tensorway/2000transistors/src/4_lines_umemory.kicad_pcb

## KiCad design src/4_lines_umemory.kicad_pcb (2023-10-25)

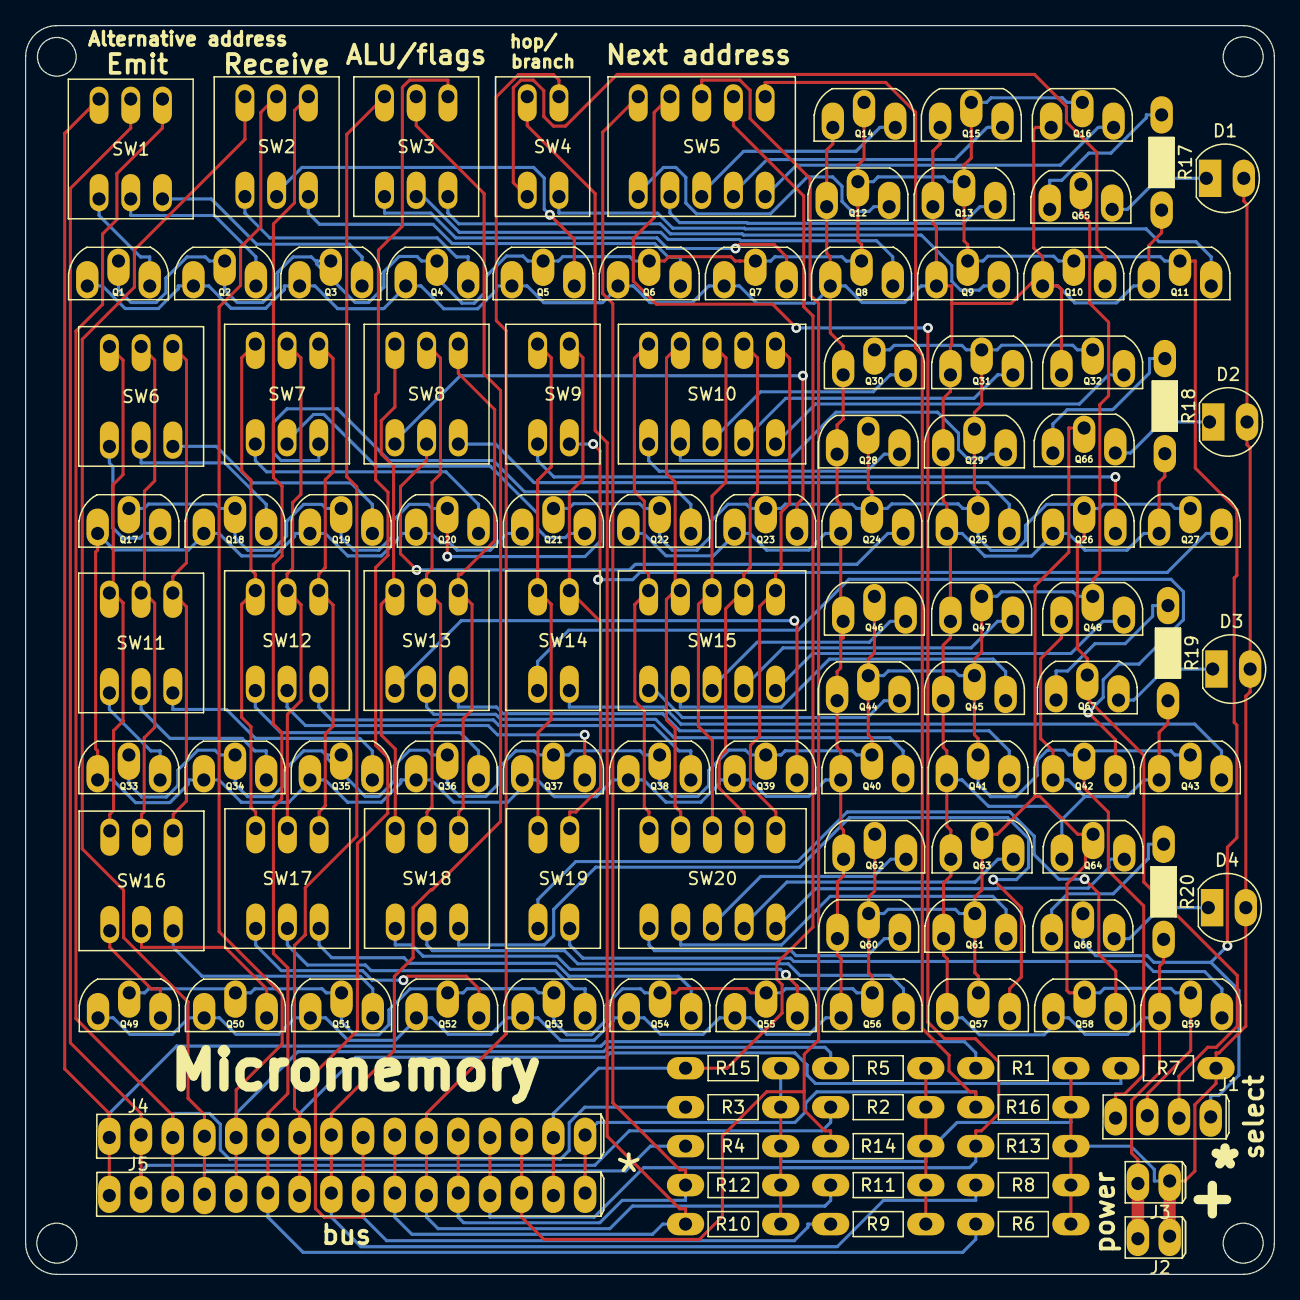
[picture p17: board 4_lines_umemory.kicad_pcb from above]

Board: 2 copper layers, 100.0 x 100.0 mm, 117 parts (0 on the bottom side), 110 nets.

Parts:
D1, D2, D3, D4: LED; led_5mm_tight
J1: Conn_01x04_Male; 4pin_tight
J2, J3: Conn_01x02_Male; 2pin_tight
J4, J5: Conn_01x16_Male; 16pin_tight
Q1, Q2, Q3, Q4, Q5, Q6, Q7, Q8, Q9, Q10, Q11, Q12, Q13, Q14, Q15, Q16, Q17, Q18, Q19, Q20, Q21, Q22, Q23, Q24, Q25, Q26, Q27, Q28, Q29, Q30, Q31, Q32, Q33, Q34, Q35, Q36, Q37, Q38, Q39, Q40, Q41, Q42, Q43, Q44, Q45, Q46, Q47, Q48, Q49, Q50, Q51, Q52, Q53, Q54, Q55, Q56, Q57, Q58, Q59, Q60, Q61, Q62, Q63, Q64, Q65, Q66, Q67, Q68: 2N7000; 2n7000_tight
R1, R2, R3, R4, R5, R6, R7, R8, R9, R10, R11, R12, R13, R14, R15, R16: R; resistor_tight
R17, R18, R19, R20: R; resistor_led_tight
SW1, SW2, SW3, SW6, SW7, SW8, SW11, SW12, SW13, SW16, SW17, SW18: SW_DIP_x03; dip3_switch
SW4, SW9, SW14, SW19: SW_DIP_x02; dip2_switch
SW5, SW10, SW15, SW20: SW_DIP_x05; dip5_switch

Connections:
+5V: D1.2, D2.2, D3.2, D4.2, J2.1, J3.1, R1.1, R2.1, R3.1, R4.1, R5.1, R6.1, R7.1, R8.1, R9.1, R10.1, R11.1, R12.1, R13.1, R14.1, R15.1, R16.1
/Sheet63D9F596/a: J4.1, J5.1, R1.2, SW1.3
/Sheet63D9F596/b: J4.2, J5.2, R2.2, SW1.2
/Sheet63D9F596/c: J4.3, J5.3, R3.2, SW1.1
/Sheet63D9F596/d: J4.4, J5.4, R4.2, SW2.3
/Sheet63D9F596/e: J4.5, J5.5, R5.2, SW2.2
/Sheet63D9F596/enable: J1.4, Q1.2, Q2.2, Q3.2, Q4.2, Q5.2, Q6.2, Q7.2, Q8.2, Q9.2, Q10.2, Q11.2, Q12.2, Q13.2, Q14.2, Q15.2, Q16.2, Q68.2
/Sheet63D9F596/f: J4.6, J5.6, R6.2, SW2.1
/Sheet63D9F596/g: J4.7, J5.7, R7.2, SW3.3
/Sheet63D9F596/h: J4.8, J5.8, R8.2, SW3.2
/Sheet63D9F596/i: J4.9, J5.9, R9.2, SW3.1
/Sheet63D9F596/j: J4.10, J5.10, R10.2, SW4.2
/Sheet63D9F596/k: J4.11, J5.11, R11.2, SW4.1
/Sheet63D9F596/l: J4.12, J5.12, R12.2, SW5.5
/Sheet63D9F596/m: J4.13, J5.13, R13.2, SW5.4
/Sheet63D9F596/n: J4.14, J5.14, R14.2, SW5.3
/Sheet63D9F596/o: J4.15, J5.15, R15.2, SW5.2
/Sheet63D9F596/p: J4.16, J5.16, R16.2, SW5.1
/sheet63DAA910/a: SW6.3, SW11.3, SW16.3
/sheet63DAA910/b: SW6.2, SW11.2, SW16.2
/sheet63DAA910/c: SW6.1, SW11.1, SW16.1
/sheet63DAA910/d: SW7.3, SW12.3, SW17.3
/sheet63DAA910/e: SW7.2, SW12.2, SW17.2
/sheet63DAA910/enable: J1.3, Q17.2, Q18.2, Q19.2, Q20.2, Q21.2, Q22.2, Q23.2, Q24.2, Q25.2, Q26.2, Q27.2, Q28.2, Q29.2, Q30.2, Q31.2, Q32.2, Q67.2
/sheet63DAA910/f: SW7.1, SW12.1, SW17.1
/sheet63DAA910/g: SW8.3, SW13.3, SW18.3
/sheet63DAA910/h: SW8.2, SW13.2, SW18.2
/sheet63DAA910/i: SW8.1, SW13.1, SW18.1
/sheet63DAA910/j: SW9.2, SW14.2, SW19.2
/sheet63DAA910/k: SW9.1, SW14.1, SW19.1
/sheet63DAA910/l: SW10.5, SW15.5, SW20.5
/sheet63DAA910/m: SW10.4, SW15.4, SW20.4
/sheet63DAA910/n: SW10.3, SW15.3, SW20.3
/sheet63DAA910/o: SW10.2, SW15.2, SW20.2
/sheet63DAA910/p: SW10.1, SW15.1, SW20.1
/sheet63DB6C5D/enable: J1.2, Q49.2, Q50.2, Q51.2, Q52.2, Q53.2, Q54.2, Q55.2, Q56.2, Q57.2, Q58.2, Q59.2, Q60.2, Q61.2, Q62.2, Q63.2, Q64.2, Q66.2
/sheet63DBEA91/enable: J1.1, Q33.2, Q34.2, Q35.2, Q36.2, Q37.2, Q38.2, Q39.2, Q40.2, Q41.2, Q42.2, Q43.2, Q44.2, Q45.2, Q46.2, Q47.2, Q48.2, Q65.2
GND: J2.2, J3.2, Q1.1, Q2.1, Q3.1, Q4.1, Q5.1, Q6.1, Q7.1, Q8.1, Q9.1, Q10.1, Q11.1, Q12.1, Q13.1, Q14.1, Q15.1, Q16.1, Q17.1, Q18.1, Q19.1, Q20.1, Q21.1, Q22.1, Q23.1, Q24.1, Q25.1, Q26.1, Q27.1, Q28.1, Q29.1, Q30.1, Q31.1, Q32.1, Q33.1, Q34.1, Q35.1, Q36.1, Q37.1, Q38.1, Q39.1, Q40.1, Q41.1, Q42.1, Q43.1, Q44.1, Q45.1, Q46.1, Q47.1, Q48.1, Q49.1, Q50.1, Q51.1, Q52.1, Q53.1, Q54.1, Q55.1, Q56.1, Q57.1, Q58.1, Q59.1, Q60.1, Q61.1, Q62.1, Q63.1, Q64.1, R17.2, R18.2, R19.2, R20.2
unnamed: D1.1, Q65.3
unnamed: D2.1, Q66.3
unnamed: D3.1, Q67.3
unnamed: D4.1, Q68.3
unnamed: Q1.3, SW1.4
unnamed: Q2.3, SW1.5
unnamed: Q3.3, SW1.6
unnamed: Q4.3, SW2.4
unnamed: Q5.3, SW2.5
unnamed: Q6.3, SW2.6
unnamed: Q7.3, SW3.4
unnamed: Q8.3, SW3.5
unnamed: Q9.3, SW3.6
unnamed: Q10.3, SW4.3
unnamed: Q11.3, SW4.4
unnamed: Q12.3, SW5.6
unnamed: Q13.3, SW5.7
unnamed: Q14.3, SW5.8
unnamed: Q15.3, SW5.9
unnamed: Q16.3, SW5.10
unnamed: Q17.3, SW6.4
unnamed: Q18.3, SW6.5
unnamed: Q19.3, SW6.6
unnamed: Q20.3, SW7.4
unnamed: Q21.3, SW7.5
unnamed: Q22.3, SW7.6
unnamed: Q23.3, SW8.4
unnamed: Q24.3, SW8.5
unnamed: Q25.3, SW8.6
unnamed: Q26.3, SW9.3
unnamed: Q27.3, SW9.4
unnamed: Q28.3, SW10.6
unnamed: Q29.3, SW10.7
unnamed: Q30.3, SW10.8
unnamed: Q31.3, SW10.9
unnamed: Q32.3, SW10.10
unnamed: Q33.3, SW11.4
unnamed: Q34.3, SW11.5
unnamed: Q35.3, SW11.6
unnamed: Q36.3, SW12.4
unnamed: Q37.3, SW12.5
unnamed: Q38.3, SW12.6
unnamed: Q39.3, SW13.4
unnamed: Q40.3, SW13.5
unnamed: Q41.3, SW13.6
unnamed: Q42.3, SW14.3
unnamed: Q43.3, SW14.4
unnamed: Q44.3, SW15.6
unnamed: Q45.3, SW15.7
unnamed: Q46.3, SW15.8
unnamed: Q47.3, SW15.9
unnamed: Q48.3, SW15.10
unnamed: Q49.3, SW16.4
unnamed: Q50.3, SW16.5
unnamed: Q51.3, SW16.6
unnamed: Q52.3, SW17.4
unnamed: Q53.3, SW17.5
unnamed: Q54.3, SW17.6
unnamed: Q55.3, SW18.4
unnamed: Q56.3, SW18.5
unnamed: Q57.3, SW18.6
unnamed: Q58.3, SW19.3
unnamed: Q59.3, SW19.4
unnamed: Q60.3, SW20.6
unnamed: Q61.3, SW20.7
unnamed: Q62.3, SW20.8
unnamed: Q63.3, SW20.9
unnamed: Q64.3, SW20.10
unnamed: Q65.1, R17.1
unnamed: Q66.1, R18.1
unnamed: Q67.1, R19.1
unnamed: Q68.1, R20.1
